wojtekbe/isfar/sidedriver/driver/tankdriver.h

#ifndef _tankdriver_h_
#define _tankdriver_h_

#define WATER_IN 1
#define WATER_OUT -1
#define MIN ((GPIOB->IDR & (1 << 10)) ? 1 : 0)
#define TANK_SPEED 75

void td_init(void);
void td_enable(void);
void td_disable(void);
void td_set_dir(int32_t);
void td_reset(void);
void td_set_pos(int);

int32_t td_cpos;
int32_t td_pos;
int32_t td_is_at_max;

int8_t td_dir;
#endif
